RoMeLaUCLA/usb2romela/firmware/Inc/main.h

#define DCD_Pin GPIO_PIN_4
#define DCD_GPIO_Port GPIOA
#define SW_Pin GPIO_PIN_1
#define SW_GPIO_Port GPIOB
#define LED_G_Pin GPIO_PIN_4
#define LED_G_GPIO_Port GPIOB
#define LED_R_Pin GPIO_PIN_5
#define LED_R_GPIO_Port GPIOB
